ZMGID/grokbot-home/services/feishu-cli/chats.md

# 飞书群（仅名称与 chat_id）

> 从 `/workspace/feishu-cli/chats.md` 摘录；**不含**消息正文、成员 open_id 列表、通讯录。
> 应用 `cli_aa430b6809f85d0c`；用户身份 王枳萌；lark-cli 1.0.97；brand feishu。

| 名称 | chat_id |
|---|---|
| 全员群 | `oc_1bfe10631cc60ae750bbc378376f3c4d` |
| bot 通知群 | `oc_ba1ec97d712cc401cabc3a09c610dcbb` |
