ZMGID/grokbot-home/bots/代码工程师/CONTEXT.md

# 代码工程师自己的记忆与项目状态

> 先读根目录 `/CONTEXT.md`。这里只记代码工程师自己的工作记录。

## 职责
- 负责 `ZMGID/Dsivio`（main，优先）和 `ZMGID/kivio` 的 CI、开着的 PR 与代码修复。
- GitHub 访问只走 `composio-pg`（Composio），不装、不要求授权官方 GitHub 连接器。

## 记录
- (2026-10-08) 用户创建本 bot（agent id `30f7829c-e287-44d7-bfdc-7c409b7da1c4`）。
- (2026-10-08) 职责定为：盯 CI 与开着的 PR，CI 挂了查根因并开修复 PR；接主 bot / 用户派来的代码任务；被问时说明 PR 或分支状态。

- (2026-10-08) Dsivio：**PR #1**（CI/release 升 Node 22）CI 全绿未合并；为同事装环境开了 **PR #2/#3/#4**（均绿未合；合并顺序建议 #3→#4，#2 独立）。另有 dsimage **PR #1**（文档），用户称 dsimage 上游不再更新、覆盖风险可忽略。v1.1.0 已发但带 `[skip ci]`。
- (2026-10-08) 用户次日重点：手工继续优化环境配置（PR #2/#3/#4 基础上）；并启动 IM Gateway（调研归小枳）。

- (2026-10-09) 用户说不需要内置 WebView2，Dsivio **PR #2 已关闭未合并**（分支保留）。随后 #1、#5（15:21）和 #3、#4（16:00/16:01）都已合入 main，Dsivio 无开着的 PR；main CI 15:21 首次转绿，合 #3/#4 后最新提交的 CI 被取消、待核实。kivio #60 仍为草稿。
