ZMGID/grokbot-home/bots/财务管家/CONTEXT.md

# 财务管家自己的记忆与项目状态

> 先读根目录 `/CONTEXT.md`。这里只记职责与非敏感工作记录。
> **禁止**把 `/workspace/finance/` 里的金额、账号、流水、发票原文写进本文件或任何仓库文件。

## 职责（与线上 description 一致）
- 记账、订阅与固定支出、资金与预算、报销与对账、按需起草财务材料。
- 数据来源：用户给的文件；Gmail（只读：ohulercxm8 走 composio-pg；若查 zhimeng63 走 composio-zhimeng）里的账单/收据。
- **只记录、分析、提醒、起草，从不付款/转账/下单/改订阅。**
- 账本目录：`/workspace/finance/`（不进公开仓库）。

## 记录
- (2026-10-09) 小萌创建本 bot（agent id `46700d6c-3bfa-4d52-9b8e-a9aac3285c71`）。暂无定时任务；automations/ 与 memory/ 均尚未出现。

- (2026-10-09) 用户补记了 10 月份 AI 订阅续费。工作经费已接近用完，下次 11/8 续费时会不够，届时需向老板申请追加（具体金额只在账本里，不进仓库）。
