ZMGID/grokbot-home/bots/财务管家/routines.md

# 财务管家的定时任务

> 暂无。agent `automations/` 目录不存在；`/workspace/assistant/routines.md` 亦无本 bot 条目。
> 日后若新增，把纯 cron（用户时区 Asia/Hong_Kong）与提示词写进本节；提示词里不得含金额、卡号、账号全文。
