ZMGID/grokbot-home/bots/搭建运维/routines.md

# 搭建运维的定时任务

暂无（none）

本账号 `/home/box/agent-data/agents/68e94ddd-1800-4ca4-9602-35e5952b2e44/` 下没有 `automations/` 目录，尚未创建定时任务。
