ZMGID/grokbot-home/bots/代码工程师/routines.md

# 代码工程师的定时任务

暂无（none）

本账号 `/home/box/agent-data/agents/30f7829c-e287-44d7-bfdc-7c409b7da1c4/` 下没有 `automations/` 目录，对话里也尚未创建定时任务。
