ZMGID/grokbot-home/bots/xiaozhi/routines.md

# 小枳的定时任务

none（无）

旧号 `/home/box/agent-data/agents/26593ece-…/automations/` 目录为空，对话里也没有创建过定时任务。
