ZMGID/grokbot-home/bots/grok-bot/notes/big-picture.md

# 大局（2026-10-08 初始化，2026-10-10 17:55 更新）
## 身份
跨境电商小公司唯一的 AI 经理兼 agent 开发。主项目 Dsivio（ZMGID/Dsivio），另管 kivio、官网、各种搭建、飞书等杂事。
## 进行中
- Dsivio：10/10 17:07 本地 main 与远端合并后直接推上 main（925d3b6，含飞书+企微 IM 集成、离线电脑控制工具和当天 5 个 IM/UI/定时任务修复），main CI 绿（已核实）；未走 PR。干净 Windows 实测、IM 真机联调仍未做。以下为 10/9 状态：10/8 发布 v1.1.0。10/9 合并 PR #1（Node 22）、#5、#3、#4（内置 Python/Node 运行时 + 国内镜像），#2 关闭，无 open PR。main CI 10/9 15:21 首次转绿，但合 #3/#4 后的 CI 被取消，最新提交 2c32892 未核实。Mac 本地 main 有 5 个未推送提交（含飞书+企微 IM 集成、离线电脑控制工具），与远端分叉（多 5 少 17），另有 16 个未提交改动（插件出表用内置环境）。干净 Windows 实测未做。
- kivio：10/9 上午 7 个修复提交，main CI 绿（10/9 13:59）。PR #60「Kivio Study 材料学习工作台」草稿，10/7 后无进展；#15、#8 老 PR 挂着。
- 官网（https://eastforceglobal.com/dsivio/，自己服务器上的 nginx 静态站）：10/8 已上线 v1.1.0 页面，安装包放在自己服务器上的 /dsivio/downloads/v1.1.0/。由搭建运维负责。
- 飞书：10/10 用 lark-cli 接好（王枳萌身份），建了全员群和 bot 通知群；运营选品群、公司手册知识库、审批精简、多维表格未做。
- grokbot-home 迁移仓库：已公开，密钥加密，仓库管家负责同步、演练和审计。
- bot 体系：10/8 搭好（代码工程师、搭建运维、事务秘书、硬件工程师（备用）、小枳、仓库管家）。
- 创作控制器（类 TourBox）：只是测试，已停止，不再跟进。
## 风险 / 注意
- Dsivio IM 改动已直接推 main 且 CI 绿，但没经过 review；后续改动建议走 PR。
- 环境配置未在干净 Windows 上验收。
- grokbot-home-private-old 仍存在（10/10 核实，含明文 Composio 密钥），密钥轮换未核实。
- 10/10 凌晨有 Devin 获得 ChatGPT 套餐额度授权、X 账号验证码和密码重置邮件，待用户确认是否本人操作。
- 小米 MiMo V2.5 系列 10/21 10:00 下线，如有使用需迁到 V2.6。
- vm-01 号池为空、请求 503（搭建运维汇报）；工作经费余额约 769 元，11/8 续费不足（财务管家汇报）。
- grokbot-home 加密口令只有 6 位数字（用户已知情并选择保留）。
## 本周方向
- 10/8 约一半时间投入 bot 和迁移基础设施；之后应回到 Dsivio 质量（CI 变绿）。

- 10/8 记录：Dsivio 新方向：① 环境配置优化（同事电脑装环境太费时间，已开 PR #2/#3/#4，10/9 用户手工继续优化，当天最重要）；② IM Gateway（接入消息平台），参考 Hermes。

- 10/9 记录：环境配置 PR 全部合入，IM 网关本地第一版完成（未推送）。下周初：推送 + main CI 转绿 → 干净 Windows 验收 → IM 真机联调。

- 10/10 记录：IM 网关推上 main 并转绿。下个工作日：干净 Windows 验收 → IM 真机联调 → 安全收尾。
