ZMGID/grokbot-home/bots/xiaozhi/raw/memory/profile.md

# About the user

<!-- Enduring facts: who the user is, how to address them, lasting preferences.
     Kept in mind every turn. Safe to read, grep, and edit.
     One fact per line, as "- (YYYY-MM-DD) <fact>". -->
- (2026-08-21) 用户在共用电脑上拉了 Kivio Desktop（github.com/ZMGID/kivio），本地路径 /workspace/kivio，main 分支，当前在做 Linux 适配。
- (2026-08-21) 用户比较常用的本地 CLI 是 Claude Code、Codex、Pi、OpenCode、DSH。
- (2026-08-26) 用户的 GitHub 账号是 ZMGID（显示名 ZhiMeng）。个人仓库 15 个，主项目 kivio；还是组织 dsh-external 的成员（约 184 个 DSH 相关私有仓库）。
- (2026-08-26) Kivio 是 Rust 项目，GitHub 约 570 star。
