ZMGID/grokbot-home/bots/xiaozhi/raw/memory/log/2026-08.md

# Memory log

<!-- Dated facts, one per line as "- (YYYY-MM-DD) <fact>". Safe to read, grep, and edit. -->
- (2026-08-21) Kivio 本地 CLI 适配正在进行：已对接 Claude、Codex、Cursor、OpenCode、Gemini、Kimi、Pi、Hermes、Grok、dsh 共 10 个，任务是对照各家近期更新找出尚未适配的缺口。
- (2026-08-21) Kivio 本地 CLI 协议分五路：Claude 走 stream-json，Codex 走 app-server，Pi 走自有 RPC，dsh 走 SDK JSON-RPC，其余（Cursor/OpenCode/Gemini/Kimi/Hermes/Grok）走 ACP；能运行中注入的只有 Codex、Pi、dsh，能原生 follow-up 的只有 Pi、dsh。
- (2026-08-21) 2026-08-21：对照 kivio 本地 CLI 适配与上游后，最高优先级缺口是 Grok 0.2.103→1.0.5（默认 Grok 4.6）、Gemini --experimental-acp 转正为 --acp（并多了 3.1/3.5）、dsh-acp 仍不可用（官方 ACP 仅 committed 文本无工具/续会话，SDK 路径正确但 rc.8 SQLite 不兼容）；其次是 Claude 2.1.220→2.1.238（5 系默认拆掉 Todo 工具）、Codex 0.149 steer 强制 expectedTurnId、Cursor 需接 ask_question/create_plan 且静态模型表已旧、ACP v2 草案不要切。
- (2026-08-21) 2026-08-21 细查常用五 CLI：Claude 2.1.238 vs 注释 2.1.220，5 系默认无 Todo 且未设 CLAUDE_CODE_ENABLE_TODO_TOOLS；Codex 0.149 已发 expectedTurnId、未发旧 profile 字段，但精选 gpt-5.6 与 live model/list 不一致、initialize 无 experimentalApi；Pi 0.84.2 steer/follow_up 已接，get_available_thinking_levels 未调；OpenCode 1.18.20 仍 ACP v1 session/load，兜底模型旧；DSH 0.1.1-rc.2，SDK+bridge 仍正确，Kivio 自管 JSON 会话不受 rc.8 SQLite 破裂影响。
- (2026-08-26) 近期在改个人仓库 fkmem（Pi 的运行时记忆，github.com/ZMGID/fkmem）。
- (2026-08-26) [note] 个人其余仓库：私有 wetware、nabai、obsidian-personal-data、Contin；公开 claude-desktop-assistant、Longtxt、ev-charging-optimization、File-Auto-Copy-Tool、openai-gemini；fork claude-tap-kivio、latex-arxiv-SKILL、hermes-agent。
- (2026-08-31) [episode] On 2026-08-21 reviewed local kivio (ZMGID/kivio, Tauri 2 + React/Rust desktop AI assistant) for local CLI adapters: mapped 10 CLIs and protocols, then rechecked Claude Code, Codex, Pi, OpenCode, and DSH against recent upstream for unadapted gaps. On 2026-08-26 listed GitHub account ZMGID’s 15 repos (recent work on fkmem and kivio) plus the dsh-external org’s 184 private DSH-plugin repos.
- (2026-08-31) [note] 用户评估他人仓库时更看重 git 时间线与 AI 痕迹，不看功能清单。
- (2026-08-31) 用户在审查他人 GitHub 作品集（DevAgent，2026-08-08 改名为 ValuSee）并要向老板做招聘汇报；口径是当会用 AI 赶 demo 的实习生面试、不要当开源作者，star/两个独立平台/Langflow contributor 从汇报拿掉。
- (2026-08-31) 被审账号 2024-08 注册、至 2026-06 无提交，公开活动从 2026-07-09 开始；作者时间被 GIT_AUTHOR_DATE 整点填过；7 月堆治理平台、8 月改成购物产品（两个名字一份 git）；8 月 9 日一天 47 个 feat/merge；172 星含牛客求 star、watcher 为 0。
