ZMGID/grokbot-home/bots/xiaozhi/raw/memory/log/2026-09.md

# Memory log

<!-- Dated facts, one per line as "- (YYYY-MM-DD) <fact>". Safe to read, grep, and edit. -->
- (2026-09-02) 用户在调研 Claude/Cursor 等把胖 skill 拆成「插件为安装单位、内含多个小 skill 为触发单位」的打包方式。
- (2026-09-02) [episode] On 2026-08-31 evaluated GitHub user biheto for a hiring report: ValuSee and DevAgent-Studio are the same AI-rushed graduation portfolio with backdated commits and solicited stars—intern interview ok, not an open-source author. On 2026-09-02 asked how agent skills are now packaged as plugins of many small trigger units rather than one fat skill, and got the Cursor/Claude plugin.json + per-skill SKILL.md pattern.
- (2026-09-02) Claude Code 与 Codex 的 skill 加载差在注入：Claude 启动只塞 name+description 目录，匹配或 / 后把整份 SKILL.md 贴进对话并常驻（references/scripts 不自动进）；Codex 只注入「name: description (file: 绝对路径)」一行、正文永不自动灌，插件须先写入 marketplace.json。
- (2026-09-02) Claude Code / Codex 插件可在根目录用 .mcp.json 随插件启动 MCP（Codex 另用 .app.json 连接已注册 MCP）；skill 与 MCP 并列，不塞进 SKILL.md。
- (2026-09-02) Claude Code 插件除 skill/MCP 还可带 commands、agents、hooks、LSP、monitors、themes、workflows、output styles、channels、bin、settings/userConfig/dependencies；Codex 目前仅 skill、MCP、.app.json、hooks、assets（apps 是已注册 MCP 映射，不是第三种运行时）。
