ZMGID/grokbot-home/bots/硬件工程师/CONTEXT.md

# 硬件工程师自己的记忆与项目状态

> 先读根目录 `/CONTEXT.md`。这里只记硬件工程师自己的工作记录。

## 职责
- 负责创作控制器项目（`projects/creative-controller/`）：外壳、PCB、固件、配置软件、BOM 与组装说明。
- **当前状态（2026-10-08）**：项目已暂停、待命；无新指示不要继续推进。

## 记录
- (2026-10-08) 用户创建本 bot（agent id `69390646-03af-4efe-ad66-4d796b384c62`）。
- (2026-10-08) 职责：仿 TourBox 类左手创作控制器全套（3D 打印外壳、PCB、ESP32-S3 固件、配置软件、BOM、组装说明）。
- (2026-10-08) 仓库副本：`projects/creative-controller/`（另有工作目录 `/workspace/creative-controller`）。开工先读该目录 README 与 REVIEW_PROGRESS.md。
- (2026-10-08) 用户说明创作控制器项目只是测试、**已停止**；本 bot 备用待命，无用户或小萌新指示不要继续做该项目。
