ZMGID/grokbot-home/projects/creative-controller/mechanical/out/knob_ring.step

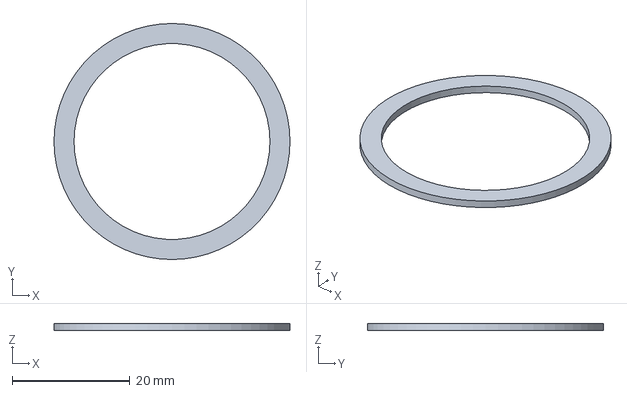
[picture p22: CAD file, 2026-10-08]
projects/creative-controller/mechanical/out/knob_ring.step
40.0 x 40.0 x 1.20 mm
