ZMGID/grokbot-home/projects/creative-controller/print/light_pipe_clearPETG.stl

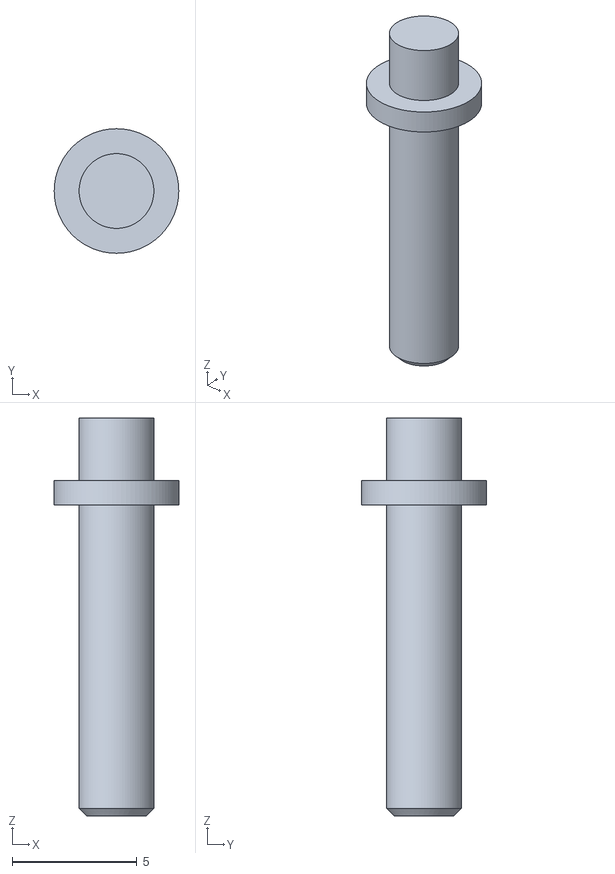
[picture p23: CAD file, 2026-10-08]
projects/creative-controller/print/light_pipe_clearPETG.stl
5.00 x 5.00 x 16.0
