ZMGID/grokbot-home/projects/creative-controller/print/pwr_slider_ext.stl

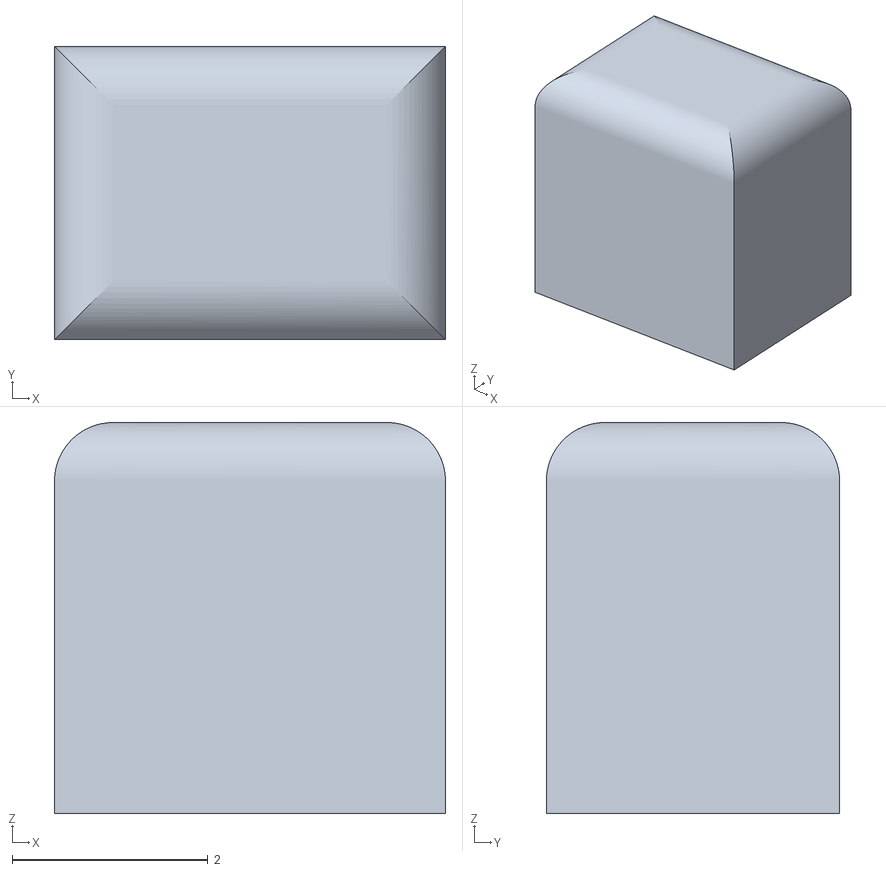
[picture p24: CAD file, 2026-10-08]
projects/creative-controller/print/pwr_slider_ext.stl
4.00 x 3.00 x 4.00
