ZMGID/grokbot-home/projects/creative-controller/print/cap_br.stl

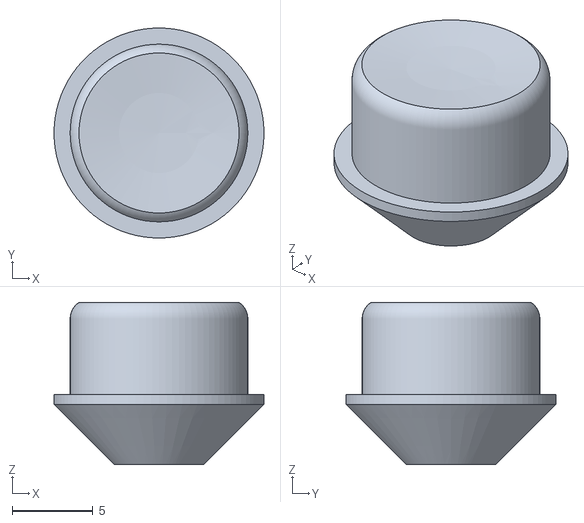
[picture p25: CAD file, 2026-10-08]
projects/creative-controller/print/cap_br.stl
13.0 x 13.0 x 10.0
