ZMGID/grokbot-home/projects/creative-controller/mechanical/out/cap_top.step

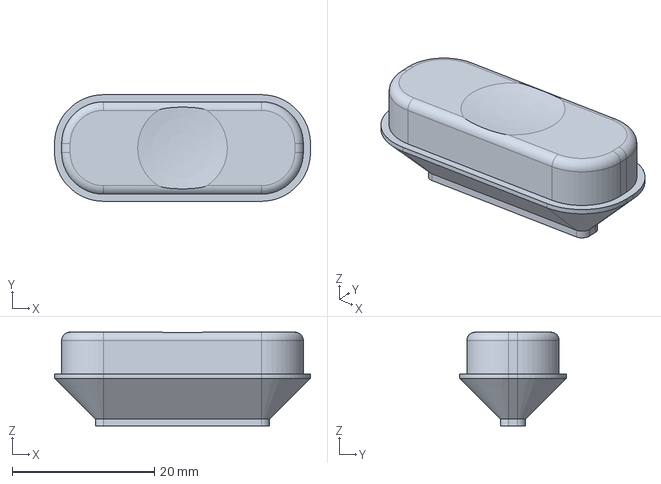
[picture p26: CAD file, 2026-10-08]
projects/creative-controller/mechanical/out/cap_top.step
36.0 x 15.0 x 13.2 mm
