ZMGID/grokbot-home/projects/creative-controller/mechanical/out/knob.step

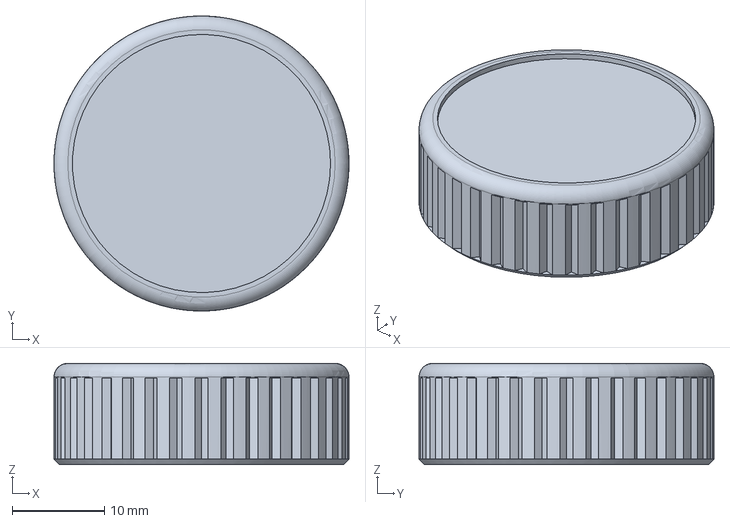
[picture p27: CAD file, 2026-10-08]
projects/creative-controller/mechanical/out/knob.step
32.0 x 32.0 x 11.0 mm
