ZMGID/grokbot-home/projects/creative-controller/print/plate0_tolerance_test.3mf

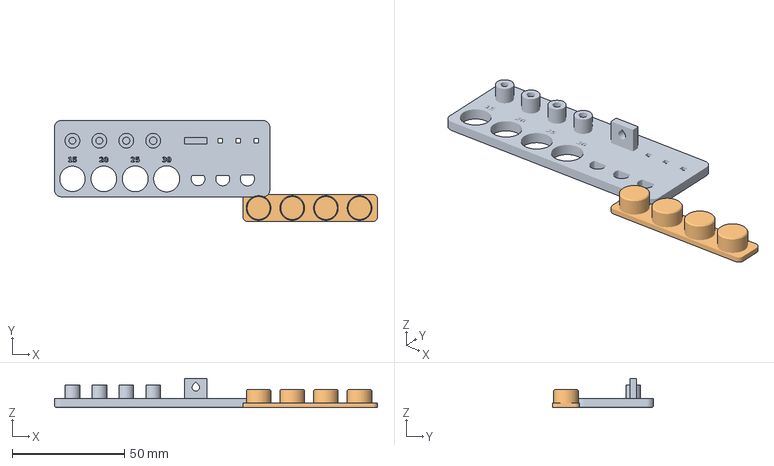
[picture p28: CAD file, 2026-10-08]
projects/creative-controller/print/plate0_tolerance_test.3mf
144.0 x 45.0 x 13.0 mm
tolerance_test_plate
tolerance_test_pegs
