ZMGID/grokbot-home/projects/creative-controller/print/plate1_shells.3mf

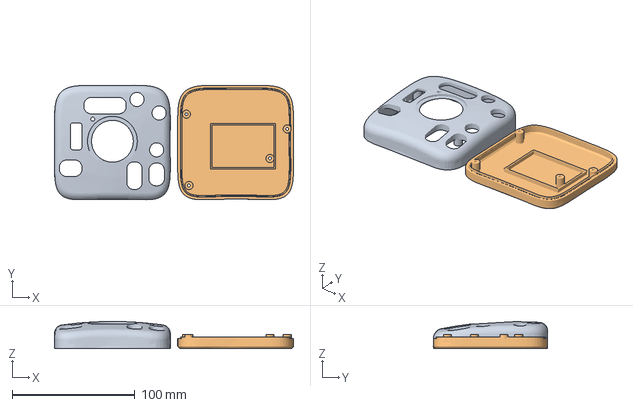
[picture p29: CAD file, 2026-10-08]
projects/creative-controller/print/plate1_shells.3mf
194.5 x 93.2 x 22.0 mm
top_shell
bottom_shell
