ZMGID/grokbot-home/projects/creative-controller/print/plate2_controls.3mf

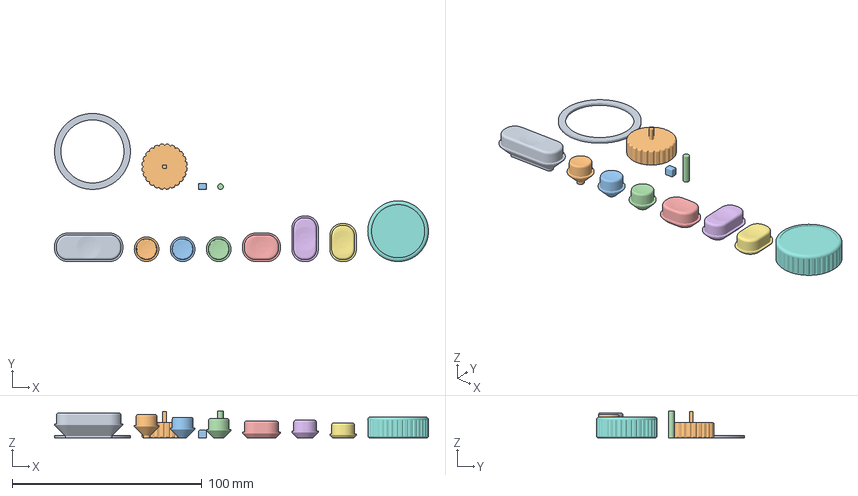
[picture p30: CAD file, 2026-10-08]
projects/creative-controller/print/plate2_controls.3mf
197.0 x 78.0 x 14.0 mm
cap_top
cap_tr1
cap_tr2
cap_br
cap_side
cap_tall1
cap_tall2
knob
knob_ring
scroll_wheel
pwr_slider_ext
wheel_pin_optional
